mirage335/aftermarket_8kX_hinge/_ref/8kX_Hinge_Pins/PhillipsHeadCamOut.jpg

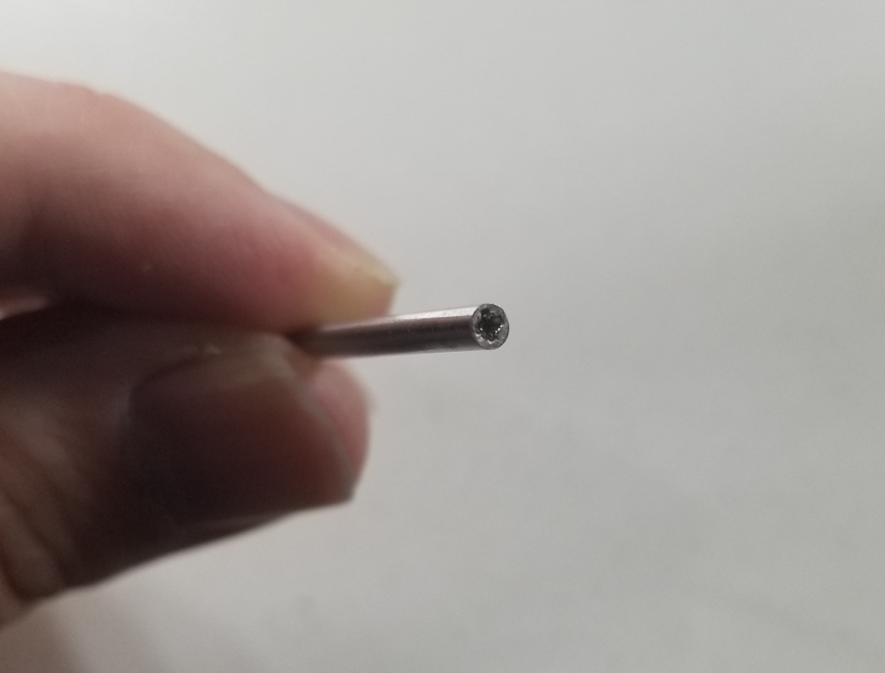
_ref/8kX_Hinge_Pins/PhillipsHeadCamOut.jpg
