mirage335/aftermarket_8kX_hinge/_ref/8kX_Hinge_Pins/UnthreadedLength.jpg

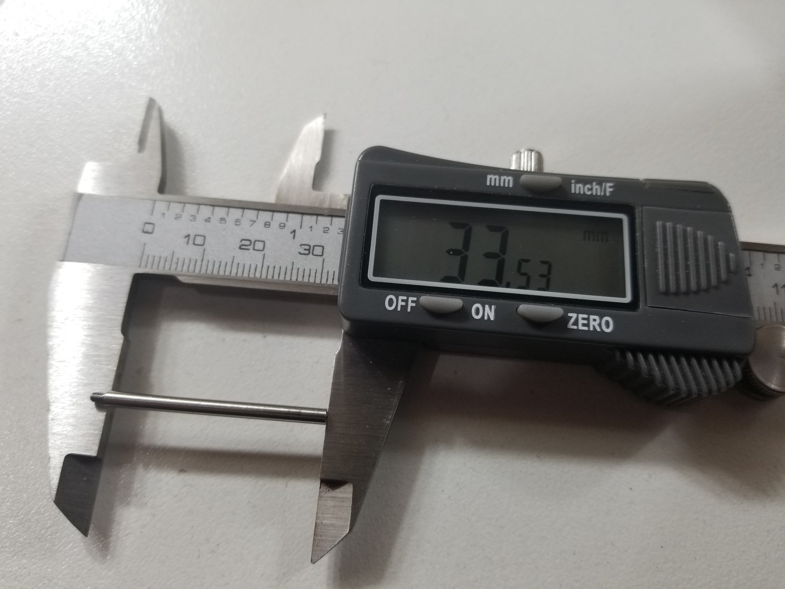
_ref/8kX_Hinge_Pins/UnthreadedLength.jpg
