mirage335/aftermarket_8kX_hinge/_ref/comparison/20201109_164940.jpg

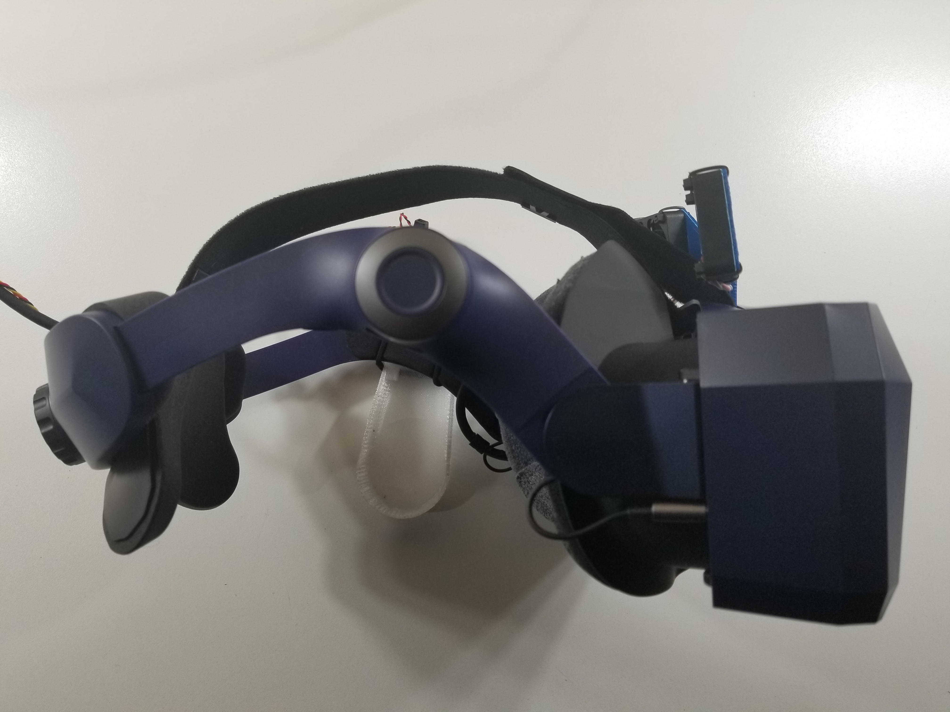
_ref/comparison/20201109_164940.jpg
