mirage335/aftermarket_8kX_hinge/_ref/comparison/20201109_165708.jpg

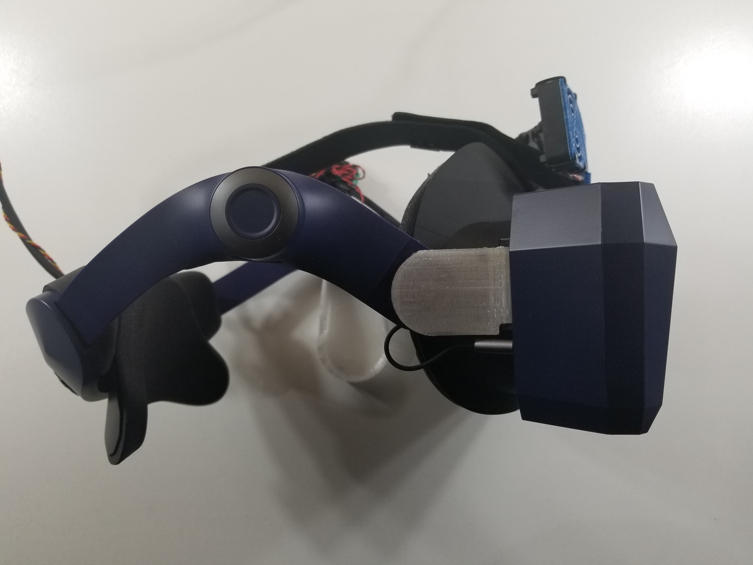
_ref/comparison/20201109_165708.jpg
