mirage335/aftermarket_8kX_hinge/_ref/comparison/20201109_171050.jpg

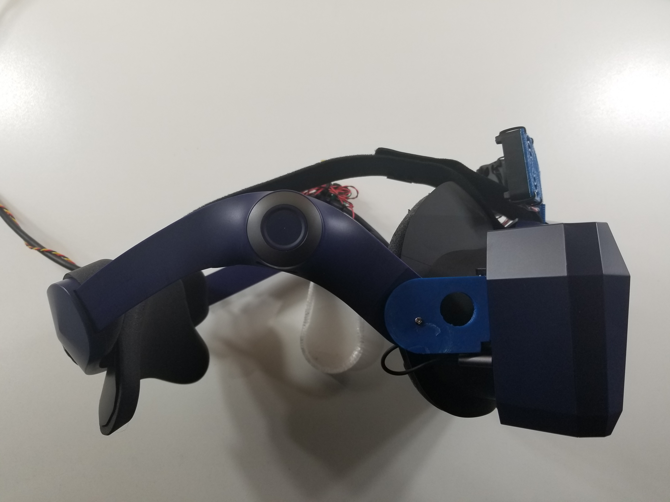
_ref/comparison/20201109_171050.jpg
