mirage335/aftermarket_8kX_hinge/platter.png

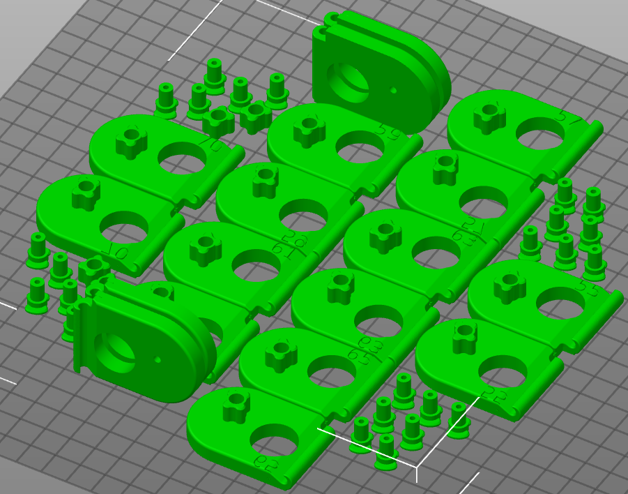
platter.png
