mirage335/aftermarket_8kX_hinge/platter.png-sliced.png

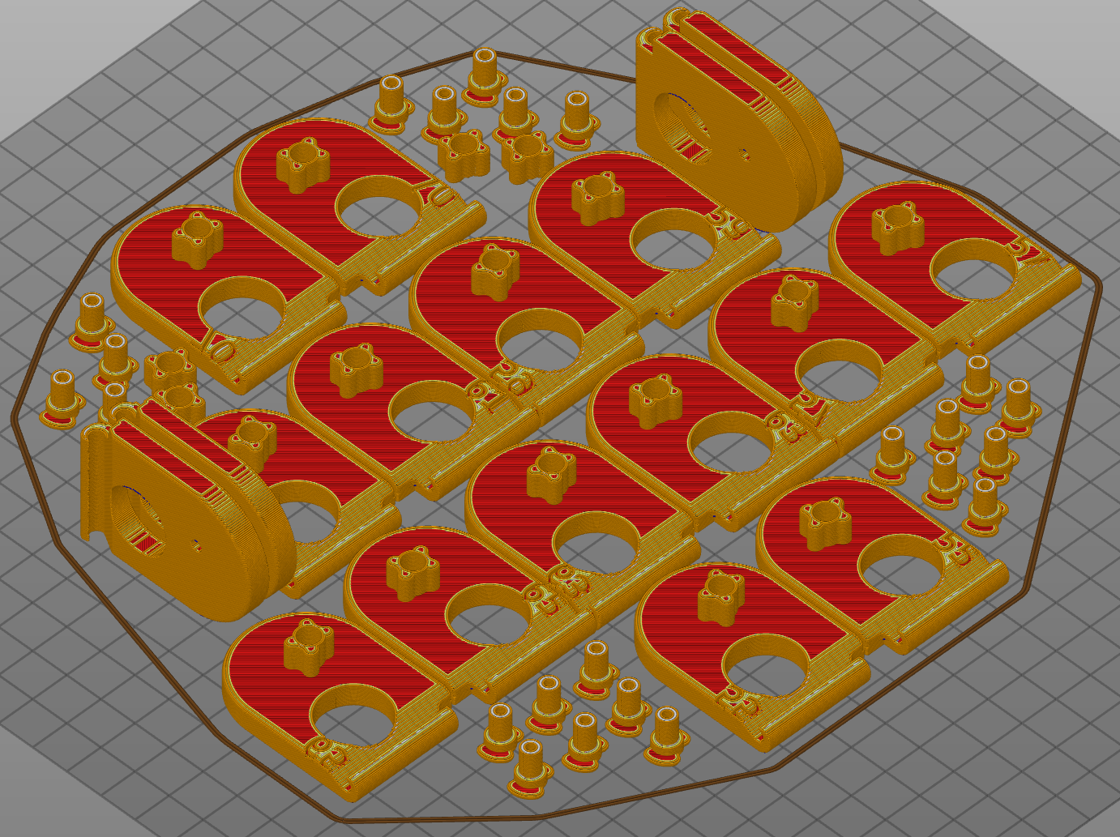
platter.png-sliced.png
